honkajan/stm32-nrf24-temperature-logger/docs/hardware/kicad/temp_logger_remote.kicad_sch

## KiCad design docs/hardware/kicad/temp_logger_remote.kicad_sch (2026-03-17)

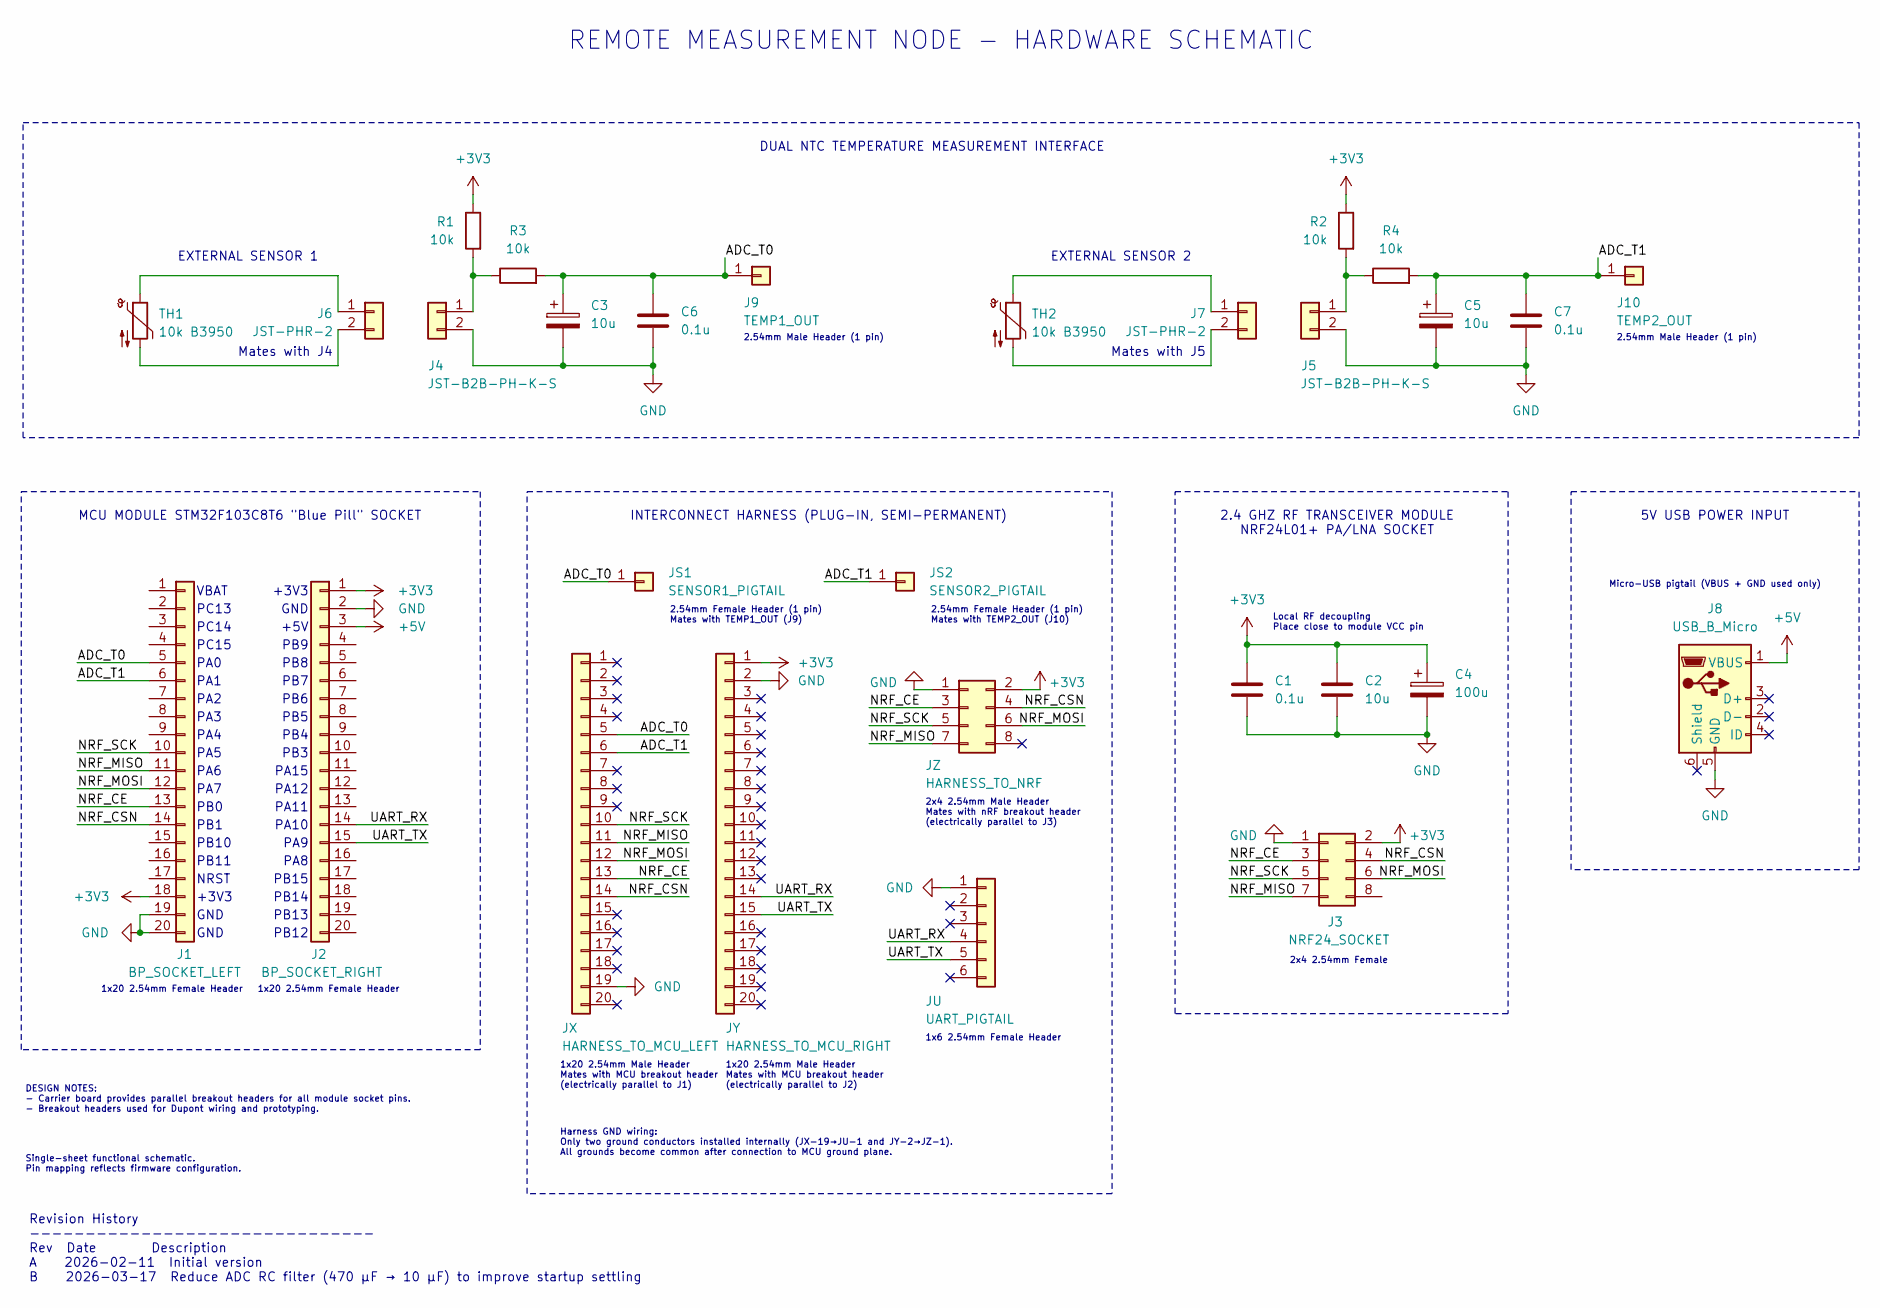
[picture p3: schematic temp_logger_remote.kicad_sch]

Parts:
C1, C6, C7: 0.1u
C2, C3, C5: 10u
C4: 100u
J1: BP_SOCKET_LEFT
J2: BP_SOCKET_RIGHT
J3: NRF24_SOCKET
J4, J5: JST-B2B-PH-K-S
J6, J7: JST-PHR-2
J8: USB_B_Micro
J9: TEMP1_OUT
J10: TEMP2_OUT
JS1: SENSOR1_PIGTAIL
JS2: SENSOR2_PIGTAIL
JU: UART_PIGTAIL
JX: HARNESS_TO_MCU_LEFT
JY: HARNESS_TO_MCU_RIGHT
JZ: HARNESS_TO_NRF
R1, R2, R3, R4: 10k
TH1, TH2: 10k B3950

Connections:
+3V3: C1.1, C2.1, C4.1, J1.18, J2.1, J3.2, JY.1, JZ.2, R1.1, R2.1
+5V: J2.3, J8.1 (VBUS)
ADC_T0: C3.1, C6.1, J1.5, J9.1, JS1.1, JX.5, R3.2
ADC_T1: C5.1, C7.1, J1.6, J10.1, JS2.1, JX.6, R4.2
GND: C1.2, C2.2, C3.2, C4.2, C5.2, C6.2, C7.2, J1.19, J1.20, J2.2, J3.1, J4.2, J5.2, J8.5 (GND), JU.1, JX.19, JY.2, JZ.1
NRF_CE: J1.13, J3.3, JX.13, JZ.3
NRF_CSN: J1.14, J3.4, JX.14, JZ.4
NRF_MISO: J1.11, J3.7, JX.11, JZ.7
NRF_MOSI: J1.12, J3.6, JX.12, JZ.6
NRF_SCK: J1.10, J3.5, JX.10, JZ.5
unnamed: J4.1, R1.2, R3.1
unnamed: J5.1, R2.2, R4.1
unnamed: J6.1, TH1.1
unnamed: J6.2, TH1.2
unnamed: J7.1, TH2.1
unnamed: J7.2, TH2.2
UART_RX: J2.14, JU.4, JY.14
UART_TX: J2.15, JU.5, JY.15

Notes on the sheet:
PA3
Single-sheet functional schematic. Pin mapping reflects firmware configuration.
Mates with J4
PA8
PB5
2.54mm Female Header (1 pin) Mates with TEMP2_OUT (J10)
VBAT
PB8
INTERCONNECT HARNESS (PLUG-IN, SEMI-PERMANENT)
EXTERNAL SENSOR 1
PB14
PA1
PA6
Local RF decoupling Place close to module VCC pin
2x4 2.54mm Female
NRST
PA11
GND
REMOTE MEASUREMENT NODE - HARDWARE SCHEMATIC
PB3
PB13
Micro-USB pigtail (VBUS + GND used only)
Revision History ------------------------------- Rev Date Description A 2026-02-11 Initial version B 2026-03-17 Reduce ADC RC filter (470 µF → 10 µF) to improve startup settling
2x4 2.54mm Male Header Mates with nRF breakout header (electrically parallel to J3)
EXTERNAL SENSOR 2
PC14
PA5
PA7
Harness GND wiring: Only two ground conductors installed internally (JX-19→JU-1 and JY-2→JZ-1). All grounds become common after connection to MCU ground plane.
1x6 2.54mm Female Header
PA12
PA2
PC15
+3V3
PB1
PA0
1x20 2.54mm Female Header
DUAL NTC TEMPERATURE MEASUREMENT INTERFACE
+5V
Mates with J5
2.54mm Male Header (1 pin)
PB7
PA9
PA4
PC13
2.54mm Female Header (1 pin) Mates with TEMP1_OUT (J9)
PB10
5V USB POWER INPUT
DESIGN NOTES: - Carrier board provides parallel breakout headers for all module socket pins. - Breakout headers used for Dupont wiring and prototyping.
PB0
PB15
MCU MODULE STM32F103C8T6 "Blue Pill" SOCKET
PB11
PB4
PA10
PA15
2.4 GHZ RF TRANSCEIVER MODULE NRF24L01+ PA/LNA SOCKET
PB6
1x20 2.54mm Male Header Mates with MCU breakout header (electrically parallel to J1)
PB9
PB12
1x20 2.54mm Male Header Mates with MCU breakout header (electrically parallel to J2)
